rrainey/agc-mechanical-cad/agc-block-ii/2004699A-001-exact.step

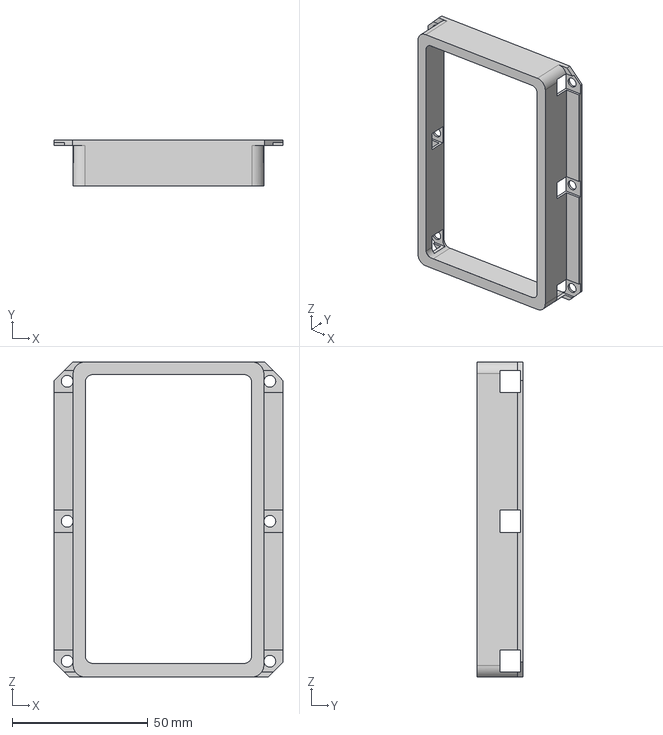
[picture p22: CAD file, 2019-06-29]
agc-block-ii/2004699A-001-exact.step
84.2 x 17.0 x 116.1 mm
