rrainey/agc-mechanical-cad/agc-block-ii/1006315G-exact.step

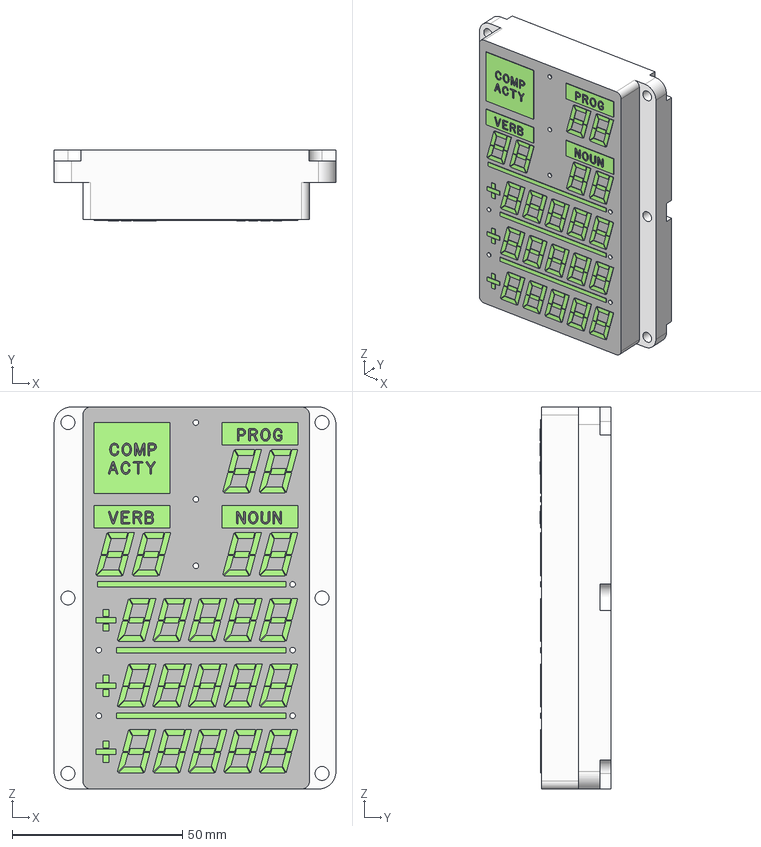
[picture p23: CAD file, 2019-06-26]
agc-block-ii/1006315G-exact.step
82.8 x 20.9 x 112.3 mm
Digit (1) x 21
