rrainey/agc-mechanical-cad/agc-block-ii/1006349-exact-GASKET, RETAINED.step

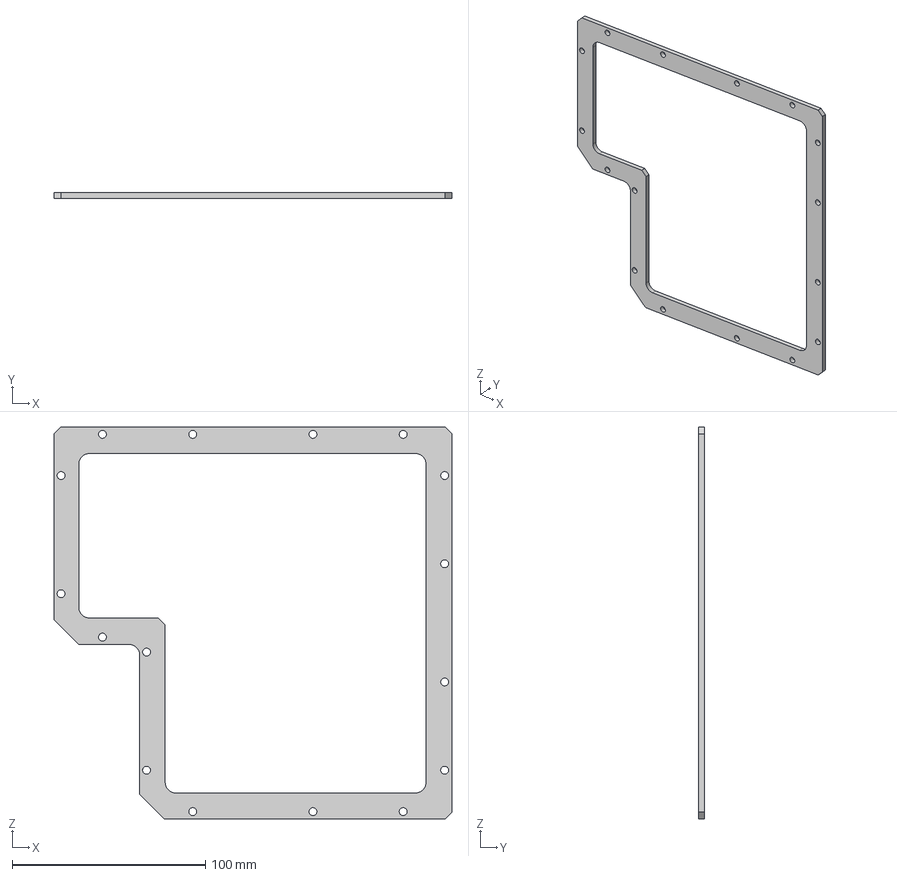
[picture p24: CAD file, 2019-06-16]
agc-block-ii/1006349-exact-GASKET, RETAINED.step
206.2 x 3.17 x 203.1 mm
